blueOkiris/Game-Card/g/Snek/Sprites.hpp

/*
 * Author: Dylan Turner
 * Description: Sprites definition for Snek. 
 */

#ifndef _SPRITES_HPP_
#define _SPRITES_HPP_

const uint8_t g_wallSprs[4][8] = {
    // Top
    {
        0b11000000,
        0b11000000,
        0b11000000,
        0b11000000,
        0b11000000,
        0b11000000,
        0b11000000,
        0b11000000,
    },
    
    // Bottom
    {
        0b00000011,
        0b00000011,
        0b00000011,
        0b00000011,
        0b00000011,
        0b00000011,
        0b00000011,
        0b00000011,
    },
    
    // Left
    {
        0b00000000,
        0b00000000,
        0b00000000,
        0b00000000,
        0b00000000,
        0b00000000,
        0b11111111,
        0b11111111
    },
    
    // Right
    {
        0b11111111,
        0b11111111,
        0b00000000,
        0b00000000,
        0b00000000,
        0b00000000,
        0b00000000,
        0b00000000
    },
};

const uint8_t g_snekHead[8] = {
    0b11111111,
    0b11111111,
    0b11111111,
    0b11111111,
    0b11111111,
    0b11111111,
    0b11111111,
    0b11111111
};

const uint8_t g_snekSpr[8] = {
    0b11111111,
    0b10000001,
    0b10000001,
    0b10000001,
    0b10000001,
    0b10000001,
    0b10000001,
    0b11111111
};

const uint8_t g_foodSpr[8] = {
    0b00000000,
    0b00011000,
    0b00100100,
    0b01000010,
    0b01000010,
    0b00100100,
    0b00011000,
    0b00000000
};

const uint8_t g_blankSpr[8] = { 0, 0, 0, 0, 0, 0, 0, 0 };

#define FONT_W      0
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
    
    // 8
    0b00000000,
    0b00110110,
    0b01001001,
    0b01001001,
    0b01001001,
    0b01001001,
    0b00110110,
    0b00000000,

    // 9
    0b00000000,
    0b01001110,
    0b10010001,
    0b10010001,
    0b10010001,
    0b10010001,
    0b01111110,
    0b00000000,
};

#endif
