blueOkiris/Game-Card/g/Ping/Sprites.hpp

/*
 * Author: Dylan Turner
 * Description: Sprites Definition for Ping
 */

#ifndef _SPRITES_HPP_
#define _SPRITES_HPP_

const uint8_t g_paddleSpr[8] = {
    0b11111111,
    0b10000001,
    0b10000001,
    0b10000001,
    0b10000001,
    0b10000001,
    0b10000001,
    0b11111111
};

extern const uint8_t g_backSprs[4][8] = {
    { 0, 0, 0, 0, 0, 0, 0, 0 },
    { 0, 0, 0, 0, 0, 0, 0, 0 },
    { 0, 0, 0, 0, 0, 0, 0, 0 },
    { 0, 0, 0, 0, 0, 0, 0, 0 }
};

const uint8_t g_ballSpr[8] = {
    0b00111100,
    0b01000010,
    0b10000001,
    0b10000001,
    0b10000001,
    0b10000001,
    0b01000010,
    0b00111100
};

#define FONT_COUNT  18
#define FONT_P      0
#define FONT_I      1
#define FONT_N      2
#define FONT_G      3
#define FONT_SPACE  4
#define FONT_DASH   5
#define FONT_H      6
#define FONT_L      7
#define FONT_0      8
#define FONT_1      9
#define FONT_2      10
#define FONT_3      11
#define FONT_4      12
#define FONT_5      13
#define FONT_6      14
#define FONT_7      15
#define FONT_W      16
#define FONT_S      17

const uint8_t g_fontSprs[FONT_COUNT][8] = {
    // P
    {
        0b00000000,
        0b01111111,
        0b00001001,
        0b00001001,
        0b00001001,
        0b00001001,
        0b00000110,
        0b00000000
    },

    // I
    {
        0b00000000,
        0b01000001,
        0b01000001,
        0b01111111,
        0b01000001,
        0b01000001,
        0b01000001,
        0b00000000
    },

    // N
    {
        0b00000000,
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
        0b00111000,
        0b01000000,
        0b00111111,
        0b00000000
    },

    // S
    {
        0b00000000,
        0b00100110,
        0b01001001,
        0b01001001,
        0b01001001,
        0b01001001,
        0b00110010,
        0b00000000
    },
};

#endif
